kesting-log/Li-Ion-Battery-Charger-PCB-Project/Schematic/Lithium-Ion Battery Charger.kicad_sch

## KiCad design Schematic/Lithium-Ion Battery Charger.kicad_sch (2024-10-09)

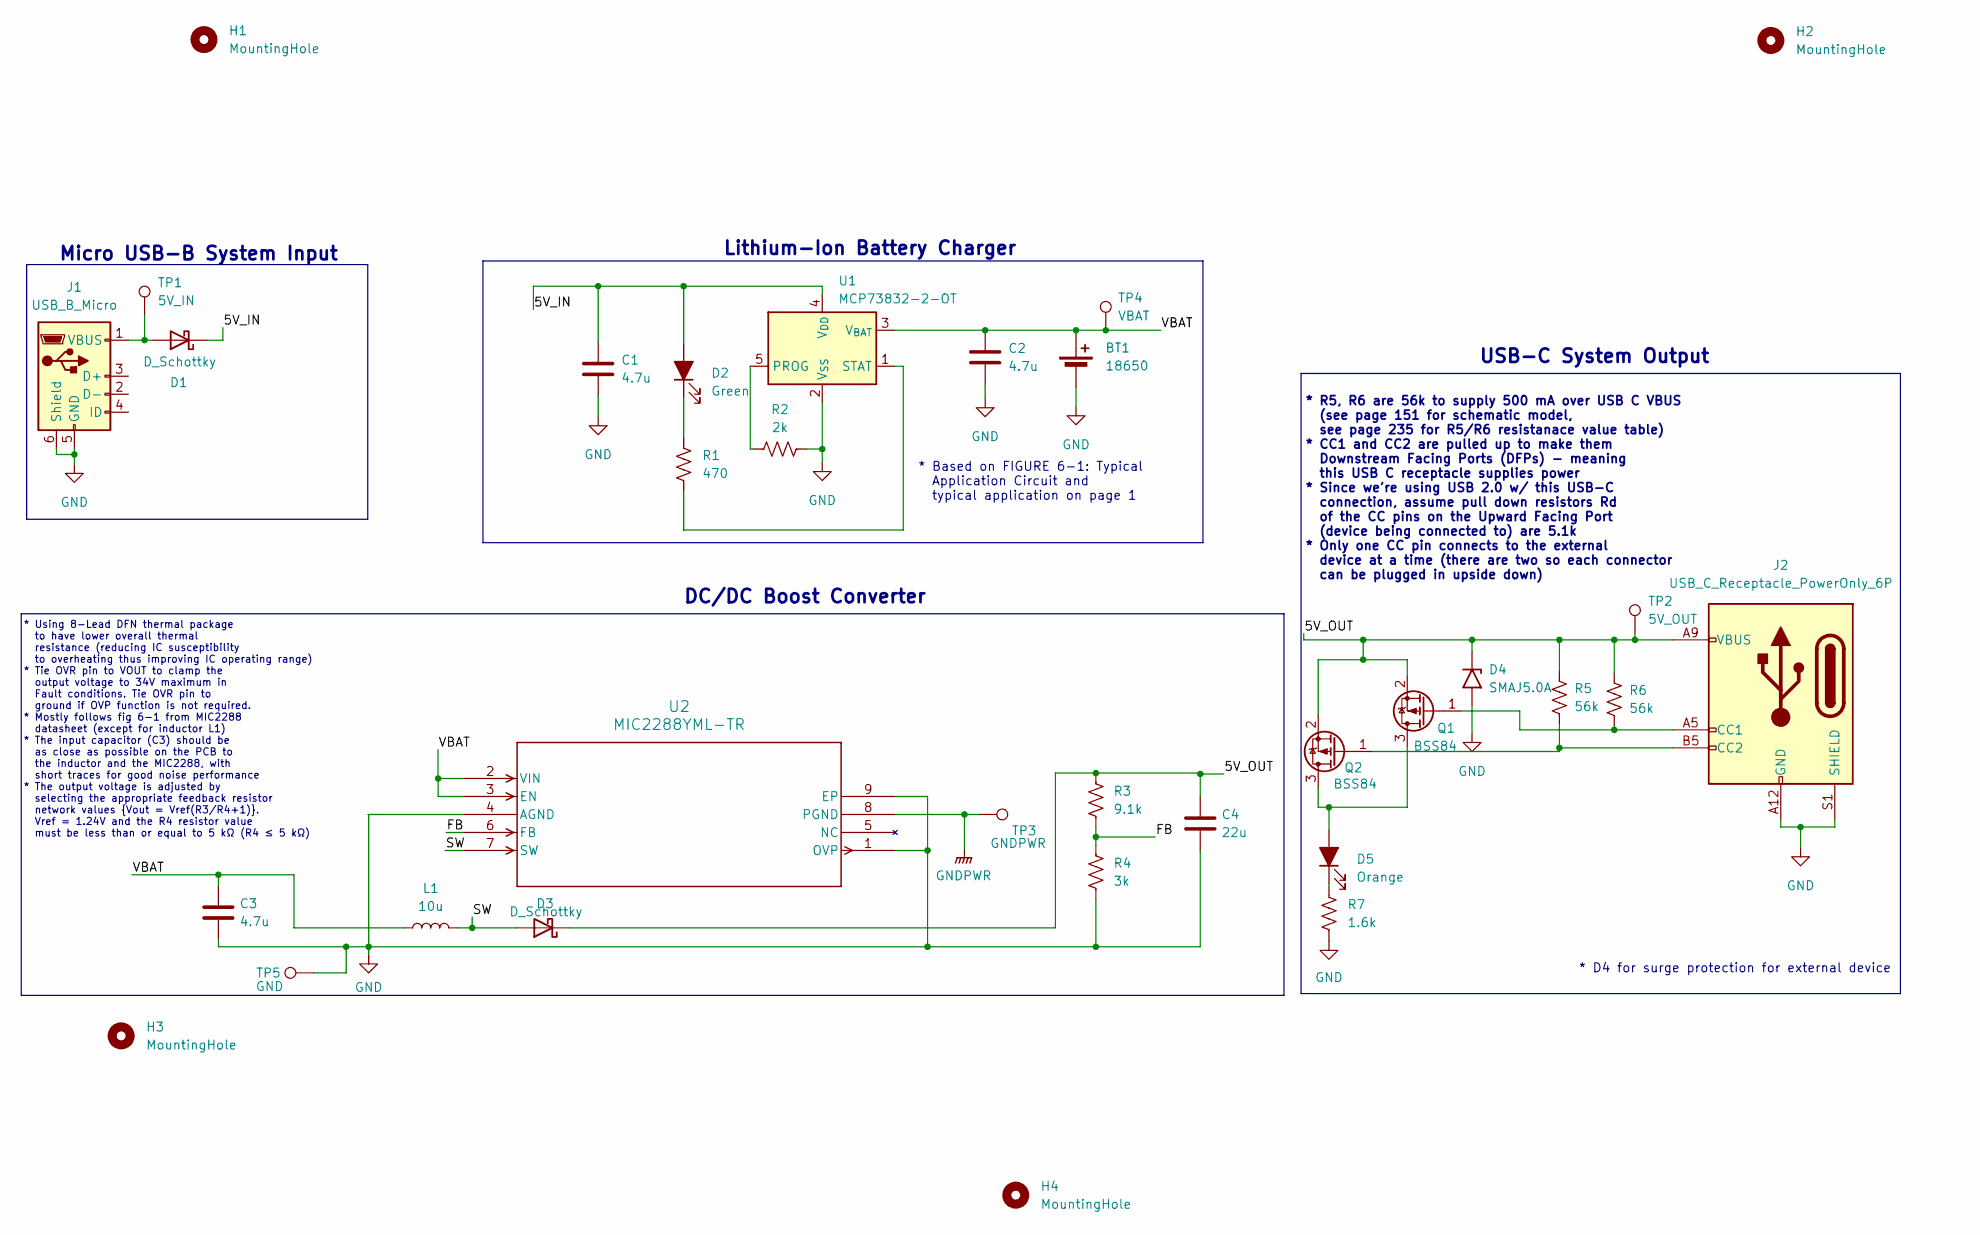
[picture p7: schematic Lithium-Ion Battery Charger.kicad_sch]

Parts:
BT1: 18650; BatteryHolder_Keystone_1042_1x18650; Digikey Part Number 36-1042-ND; 1568-1488-ND
C1, C2, C3: 4.7u; C_1812_4532Metric_Pad1.57x3.40mm_HandSolder; Digikey Part Number 399-14738-1-ND
C4: 22u; C_1206_3216Metric_Pad1.33x1.80mm_HandSolder; Digikey Part Number 478-KGM31HR50J226KUCT-ND
D1, D3: D_Schottky; D_1206_3216Metric_Pad1.42x1.75mm_HandSolder; Digikey Part Number 478-7806-1-ND
D2: Green; LED_1206_3216Metric_Pad1.42x1.75mm_HandSolder; Digikey Part Number 1080-1419-1-ND
D4: SMAJ5.0A; D_SMA; Digikey Part Number SMAJ5.0ALFCT-ND
D5: Orange; LED_1206_3216Metric_Pad1.42x1.75mm_HandSolder; Digikey Part Number 754-1941-1-ND
H1, H2, H3, H4: MountingHole; MountingHole_3mm
J1: USB_B_Micro; USB_Micro-B_Amphenol_10104110_Horizontal; Digikey Part Number 609-4052-1-ND
J2: USB_C_Receptacle_PowerOnly_6P; USB_C_Receptacle_GCT_USB4135-GF-A_6P_TopMnt_Horizontal; Digikey Part Number 2073-USB4135-GF-ACT-ND
L1: 10u; L_Abracon_ASPI-4030S; Digikey Part Number 535-12314-1-ND
Q1, Q2: BSS84; SOT-23; Digikey Part Number 1727-2931-1-ND
R1: 470; R_1206_3216Metric_Pad1.30x1.75mm_HandSolder; Digikey Part Number A106077CT-ND
R2: 2k; R_1206_3216Metric_Pad1.30x1.75mm_HandSolder; Digikey Part Number 311-2.00KFRCT-ND
R3: 9.1k; R_1206_3216Metric_Pad1.30x1.75mm_HandSolder; Digikey Part Number 2019-RK73H2BTTD9101FCT-ND
R4: 3k; R_1206_3216Metric_Pad1.30x1.75mm_HandSolder; Digikey Part Number 311-3.00KFRCT-ND
R5, R6: 56k; R_1206_3216Metric_Pad1.30x1.75mm_HandSolder; Digikey Part Number RMCF1206JT56K0CT-ND
R7: 1.6k; R_1206_3216Metric_Pad1.30x1.75mm_HandSolder; Digikey Part Number 311-1.60KFRCT-ND
TP1: 5V_IN; TestPoint_THTPad_D2.5mm_Drill1.2mm; Digikey Part Number 36-5001-ND
TP2: 5V_OUT; TestPoint_THTPad_D2.5mm_Drill1.2mm; Digikey Part Number 36-5001-ND
TP3: GNDPWR; TestPoint_THTPad_D2.5mm_Drill1.2mm; Digikey Part Number 36-5001-ND
TP4: VBAT; TestPoint_THTPad_D2.5mm_Drill1.2mm; Digikey Part Number 36-5001-ND
TP5: GND; TestPoint_THTPad_D2.5mm_Drill1.2mm; Digikey Part Number 36-5001-ND
U1: MCP73832-2-OT; SOT-23-5_HandSoldering; Digikey Part Number MCP73832T-2DCI/OTCT-ND
U2: MIC2288YML-TR; MLF-8_ML_MCH; Digikey Part Number 576-1075-1-ND

Connections:
5V_IN: C1.1, D1.1 (K), D2.2 (A), U1.4 (V_{DD})
5V_OUT: C4.1, D3.1 (K), D4.1 (A1), J2.A9 (VBUS), J2.B9 (VBUS), Q1.2 (S), Q2.2 (S), R3.1, R5.1, R6.1, TP2.1
FB: R3.2, R4.1, U2.6 (FB)
GND: BT1.2 (-), C1.2, C2.2, C3.2, C4.2, D4.2 (A2), J1.5 (GND), J1.6 (Shield), J2.A12 (GND), J2.B12 (GND), J2.S1 (SHIELD), R2.2, R4.2, R7.2, TP5.1, U1.2 (V_{SS}), U2.1 (OVP), U2.4 (AGND), U2.9 (EP)
GNDPWR: TP3.1, U2.8 (PGND)
unnamed: D1.2 (A), J1.1 (VBUS), TP1.1
unnamed: D2.1 (K), R1.1
unnamed: D5.1 (K), R7.1
unnamed: D5.2 (A), Q1.3 (D), Q2.3 (D)
unnamed: J2.A5 (CC1), Q1.1 (G), R6.2
unnamed: J2.B5 (CC2), Q2.1 (G), R5.2
unnamed: R1.2, U1.1 (STAT)
unnamed: R2.1, U1.5 (PROG)
SW: D3.2 (A), L1.2, U2.7 (SW)
VBAT: BT1.1 (+), C2.1, C3.1, L1.1, TP4.1, U1.3 (V_{BAT}), U2.2 (VIN), U2.3 (EN)

Notes on the sheet:
USB-C System Output
* R5, R6 are 56k to supply 500 mA over USB C VBUS (see page 151 for schematic model, see page 235 for R5/R6 resistanace value table) * CC1 and CC2 are pulled up to make them Downstream Facing Ports (DFPs) - meaning this USB C receptacle supplies power * Since we're using USB 2.0 w/ this USB-C conne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
Lithium-Ion Battery Charger
* Using 8-Lead DFN thermal package to have lower overall thermal resistance (reducing IC susceptibility to overheating thus improving IC operating range) * Tie OVR pin to VOUT to clamp the output voltage to 34V maximum in Fault conditions. Tie OVR pin to ground if OVP function is not required. * Mo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
* Based on FIGURE 6-1: Typical Application Circuit and typical application on page 1
DC/DC Boost Converter
* D4 for surge protection for external device
Micro USB-B System Input
